scttnlsn/pack-monitor/src/events.h

#ifndef __EVENTS_H__
#define __EVENTS_H__

#include "pico/stdlib.h"

typedef enum {
    EVENT_TYPE_CONNECTED,
    EVENT_TYPE_DISCONNECTED,
    EVENT_TYPE_INTERVAL,
    EVENT_TYPE_REGISTER_UPDATED,
    EVENT_TYPE_CELL_UPDATED,
} event_type_t;

typedef struct {
    event_type_t event_type;
    union {
        // EVENT_TYPE_REGISTER_UPDATED
        struct {
            uint16_t reg;
            uint16_t previous_value;
            uint16_t current_value;
        } reg_info;

        // EVENT_TYPE_CELL_UPDATED
        uint8_t cell_address;
    };
} event_t;

void events_init();
bool events_enqueue(event_t event);
bool events_dequeue(event_t *event);

#endif
